MiSTer-devel/CoCo2_MiSTer/rtl/fdc.sv

////////////////////////////////////////////////////////////////////////////////
// Project Name:	COCO3 Targeting MISTer 
// File Name:		fdc.sv
//
// Floppy Disk Controller for MISTer
//
////////////////////////////////////////////////////////////////////////////////
//
// Code based partily on work by Gary Becker
// Copyright (c) 2008 Gary Becker (gary_l_becker@yahoo.com)
//
// Floopy Disk Controller (fdc.v) by Stan Hodge (stan.pda@gmail.com)
// Copyright (c) 2021 by Stan Hodge (stan.pda@gmail.com)
//
// All rights reserved

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
// Redistributions in synthesized form must reproduce the above copyright
// notice, this list of conditions and the following disclaimer in the
// documentation and/or other materials provided with the distribution.
//
// Neither the name of the author nor the names of other contributors may
// be used to endorse or promote products derived from this software without
// specific prior written permission.
//
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
// Please report bugs to the author, but before you do so, please
// make sure that this is not a derivative work and that
// you have the latest version of this file.
//
////////////////////////////////////////////////////////////////////////////////
////////////////////////////////////////////////////////////////////////////////



module fdc(
	input        		CLK,     		// clock
	input        		RESET_N,	   	// async reset
	input					dragon,			// Coco or Dragon ?
	input  		[1:0]	ADDRESS,       	// i/o port addr [extended for coco]
	input  		[7:0]	DATA_IN,        // data in
	output 		[7:0] DATA_HDD,      	// data out
	output       		HALT,         	// DMA request
	output       		NMI_09,
	output       		FIRQ,


	input				FF40_CLK,		// FDC Write support
	input				FF40_ENA,

	input				FF40_RD,		// FDC Read Data support
	input				WD1793_RD,

	input				WD1793_WR_CTRL,	// 1793 RD & WR control signal generation
	input				WD1793_RD_CTRL,

// 	SD block level interface

	input 		[3:0]	img_mounted, 	// signaling that new image has been mounted
	input				img_readonly, 	// mounted as read only. valid only for active bit in img_mounted
	input 		[19:0] 	img_size,    	// size of image in bytes. 1MB MAX!

	output		[31:0] 	sd_lba[4],
	output		[5:0]	sd_blk_cnt[4],	// number of blocks-1, total size ((sd_blk_cnt+1)*(1<<(BLKSZ+7))) must be <= 16384!
	output reg	[3:0]	sd_rd,
	output reg  [3:0]	sd_wr,
	input       [3:0]	sd_ack,

// 	SD byte level access. Signals for 2-PORT altsyncram.
	input  		[8:0]	sd_buff_addr,
	input  		[7:0] 	sd_buff_dout,
	output 		[7:0] 	sd_buff_din[4],
	input        		sd_buff_wr
	
);

wire	[7:0]	DRIVE_SEL_EXT;
wire			MOTOR;
wire			WRT_PREC;
wire			DENSITY;
wire			HALT_EN;


// Generate a 8.333 Mhz enable for the fdc... and control writes 
// Dragon needs a 1.5 Mhz clock

wire ena_8Mhz ; 
wire [6:0] fdc_clk_dvd ;
wire [5:0]	div_8mhz;

// yet another poorly documented difference between Dragon and CoCo2 : clock of the disk controller is 8Mhz for Coco and 1.5Mhz for Dragon
assign fdc_clk_dvd = (dragon ) ? 6'd38 : 6'd6 ;
assign ena_8Mhz = (div_8mhz == fdc_clk_dvd) ? 1'b1: 1'b0;

always@(negedge CLK or negedge RESET_N)
begin
	if (~RESET_N)	div_8mhz <= 6'd0;
	else
		begin
			if (ena_8Mhz)
				div_8mhz <= 6'd0;
			else
				div_8mhz <= div_8mhz + 6'd1;
		end
end


wire	[7:0]	FF40_READ_VALUE =  {HALT_EN, DRIVE_SEL_EXT[3], DENSITY, WRT_PREC, MOTOR,	DRIVE_SEL_EXT[2:0]};

//FDC read data path.  =$ff40 or wd1793(s)
assign	DATA_HDD =		(FF40_RD)							?	FF40_READ_VALUE:
						(WD1793_RD)							?	DATA_1793: //(1793[s])
																8'h00;

// $ff40 control register [part 1]

wire	[3:0]	DRIVE_SEL_EXT_PRE = {DATA_IN[6], DATA_IN[2:0]};
reg		[2:0]	drive_index;

// SD blk system is a array of 4 systems - one for each drive.  
// To keep disk track memory, we created 4 wd1793's to match the sd block interfaces
// For the interface back to the coco - we need to isolate the wd1793 the computer is talking
// to and route those feedback signals back to the coco.  This is accomplished via the drive
// select.  'drive_index' identifies which controller is addressd.


always @(negedge FF40_CLK or negedge RESET_N)
begin
	if(!RESET_N)
	begin
		DRIVE_SEL_EXT <= 8'h00;
		MOTOR <= 1'b0;
		WRT_PREC <= 1'b0;
		DENSITY <= 1'b0;
		drive_index <= 3'b000; 
	end else
	begin
		if (FF40_ENA)
		begin
			if (dragon) 
			begin
//				drive_index <= { ~DATA_IN[2], DATA_IN[1:0] } ; //bit2='0 means no drive selected and no motor 
				drive_index <= { 1'b0, DATA_IN[1:0] } ; // SRH & jF removed motor from causing selects to be out of range 
				MOTOR <= DATA_IN[2];
				DRIVE_SEL_EXT <= DATA_IN ; // only for DRIVE_SEL_EXT[3] for double-density 
				DENSITY <= DATA_IN[5] ;
			end else begin
				DRIVE_SEL_EXT <= 	{4'b0000,
									DATA_IN[6],		// Drive Select [3] / Side Select
									DATA_IN[2:0]};	// Drive Select [2:0]
				MOTOR <= DATA_IN[3];				// Turn on motor, not used here just checked, 0=MotorOff 1=MotorOn
				WRT_PREC <= DATA_IN[4];				// Write Precompensation, not used here
				DENSITY <= DATA_IN[5];				// Density, not used here just checked
				case(DRIVE_SEL_EXT_PRE)
				4'b1000:
					drive_index <= 3'd3;

				4'b0100:
					drive_index <= 3'd2;
			
				4'b0010:
					drive_index <= 3'd1;
				
				4'b0001:
					drive_index <= 3'd0;
				
				4'b1100:
					drive_index <= 3'd2;
				
				4'b1010:
					drive_index <= 3'd1;
				
				4'b1001:
					drive_index <= 3'd0;

				default:
					drive_index <= 3'd0;
				endcase
			end
		end
	end
end

// $ff40 control register [part 2]
always @(negedge FF40_CLK or negedge HALT_EN_RST)
begin
	if(!HALT_EN_RST)
	begin
		HALT_EN <= 1'b0;
	end
	else
	begin
		if (FF40_ENA)
		begin
			HALT_EN <= DATA_IN[7];					// Normal Halt enable, 0=Disabled 1=Enabled
		end
	end
end


// Control signals for the wd1793

wire 			INTRQ[4];
wire			DRQ[4];
wire			selected_DRQ;
wire			selected_INTRQ;

wire			WR[4];
wire			RD[4];
wire			RD_E[4];
//wire			CE;
wire			HALT_EN_RST;
wire	[7:0]	DATA_1793;
wire	[7:0]	dout[4];
reg				read;
reg				write;
reg 			read_d;
reg				write_d;
reg		[7:0]	DATA_IN_L;
reg				r_w_active;
reg				clk_8Mhz_enable_found;
reg				read1;
reg				write1;
reg		[1:0]	ADDRESS_L;

assign RD[0] = (read || RD_E[0])  && (drive_index == 3'd0);
assign RD[1] = (read || RD_E[1])  && (drive_index == 3'd1);
assign RD[2] = (read || RD_E[2])  && (drive_index == 3'd2);
assign RD[3] = (read || RD_E[3])  && (drive_index == 3'd3);

// The idea here is to "stretch" the CPU read and write signals to ensure we catch a 8 mhz enable.
// For writes we will buffer the data out to ensure it does not go away.
// For reads it is expected that data is available asynchronusly at the cpu rate and the only reason to catch a 
// 8Mhz edge is to update pointer and misc flags. 

// This is very nasty code and will likely only work with the present CPU timing.
// It is heavily dependant on address and write data being available just after
// the previous cycle.

always @(negedge CLK or negedge RESET_N)
begin
	if(!RESET_N)
	begin
		read_d <= 1'b0;
		write_d <= 1'b0;
		r_w_active <= 1'b0;
		clk_8Mhz_enable_found <= 1'b0;
		WR[0] <= 1'b0;
		WR[1] <= 1'b0;
		WR[2] <= 1'b0;
		WR[3] <= 1'b0;
		RD_E[0] <= 1'b0;
		RD_E[1] <= 1'b0;
		RD_E[2] <= 1'b0;
		RD_E[3] <= 1'b0;
		read1 <= 1'b0;
		write1 <= 1'b0;
		read <= 1'b0;
		write <= 1'b0;
	end
	else
	begin

//		synchronizers
		read1 <= WD1793_RD_CTRL;
		read <= read1;
		
		write1 <= WD1793_WR_CTRL;
		write <= write1;

//		delays for edge detection
		read_d <= read;
		write_d <= write;

		if ((read1 & ~read) | (write1 & ~write))
		begin
//			Latch Address & Data
			ADDRESS_L <= ADDRESS[1:0];
			DATA_IN_L <= DATA_IN;
		end
		
//		Synchronus rising edge of write
		if ((write == 1'b1) && (write_d == 1'b0))
		begin
//			Set Writes
			r_w_active <= 1'b1;
			if (ADDRESS[1:0]==2'b00)
				case (drive_index)
					3'd0:
						WR[0] <= 1'b1;
					3'd1:
						WR[1] <= 1'b1;
					3'd2:
						WR[2] <= 1'b1;
					3'd3:
						WR[3] <= 1'b1;
				endcase 
			else 
			begin // FLYNN : if not a command, write the register in ALL fdc components.
				WR[0] <= 1'b1;
				WR[1] <= 1'b1;
				WR[2] <= 1'b1;
				WR[3] <= 1'b1;
			end
		end

//		Synchronus rising edge of read
		if ((read == 1'b1) && (read_d == 1'b0))
		begin
			r_w_active <= 1'b1;
			case (drive_index)
				3'd0:
					RD_E[0] <= 1'b1;
				3'd1:
					RD_E[1] <= 1'b1;
				3'd2:
					RD_E[2] <= 1'b1;
				3'd3:
					RD_E[3] <= 1'b1;
			endcase
		end

//		Clears
		if (ena_8Mhz && r_w_active)
			clk_8Mhz_enable_found <= 1'b1;

//		1 50Mhz clock later...
		if (clk_8Mhz_enable_found)
		begin
			clk_8Mhz_enable_found <= 1'b0;
			r_w_active <= 1'b0;
			
			WR[0] <= 1'b0;
			WR[1] <= 1'b0;
			WR[2] <= 1'b0;
			WR[3] <= 1'b0;

			RD_E[0] <= 1'b0;
			RD_E[1] <= 1'b0;
			RD_E[2] <= 1'b0;
			RD_E[3] <= 1'b0;
		end
	end
end


//	NMI from disk controller
//	Selected INTRQ
assign	selected_INTRQ	=	(drive_index == 3'd0)	?	INTRQ[0]:
							(drive_index == 3'd1)	?	INTRQ[1]:
							(drive_index == 3'd2)	?	INTRQ[2]:
							(drive_index == 3'd3)	?	INTRQ[3]:
														1'b0;

assign	NMI_09	=  DENSITY & selected_INTRQ;				// DENSITY is just the IRQ mask : Send NMI if allowed (Halt Mode)

//	HALT from disk controller
//	Selected DRQ
assign FIRQ = selected_DRQ;

assign	selected_DRQ	=	(drive_index == 3'd0)	?	DRQ[0]:
							(drive_index == 3'd1)	?	DRQ[1]:
							(drive_index == 3'd2)	?	DRQ[2]:
							(drive_index == 3'd3)	?	DRQ[3]:
														1'b0;

assign	HALT	=	HALT_EN & ~selected_DRQ;

assign	HALT_EN_RST = RESET_N & ~selected_INTRQ; // From controller schematic

// Data bus selection
assign	DATA_1793 	=		(drive_index == 3'd0)	?	dout[0]:
							(drive_index == 3'd1)	?	dout[1]:
							(drive_index == 3'd2)	?	dout[2]:
							(drive_index == 3'd3)	?	dout[3]:
														8'd0;

// The SD_BLK interface and thus the wd1793 will allways transfer 1 blk. This is blk qty - 1 per spec.
assign sd_blk_cnt[3] = 6'd0;
assign sd_blk_cnt[2] = 6'd0;
assign sd_blk_cnt[1] = 6'd0;
assign sd_blk_cnt[0] = 6'd0;

reg       drive_wp[4];
reg       [3:0] drive_ready  = 4'B0;
reg       [3:0] double_sided = 4'B0;

wire [3:0] img_mounted_d ;

// As drives are mounted in MISTer this logic saves the write protect and generates ready for
// changing drives to the wd1793.
// This can also get the disk size to properly handle DS drives - TBD

// Reset of drive wp to a default of 1 removed because of persistance.

// Drive 0

always @(negedge CLK)
begin
   img_mounted_d[0] <= img_mounted[0] ;
	if (img_mounted[0] & ~img_mounted_d[0]) begin
		drive_wp[0] <= img_readonly;
		drive_ready[0] <= (img_size!=20'd0) ; 
		// drive_ready[0] <= 1'b1;
		double_sided[0]<= img_size > 20'd368600;//20'd368640;
	end
end

// Drive 1

always @(negedge CLK)
begin
   img_mounted_d[1] <= img_mounted[1] ;
	if (img_mounted[1] & ~img_mounted_d[1]) begin
		drive_wp[1] <= img_readonly;
		drive_ready[1] <= (img_size!=20'd0) ; 
		double_sided[1]<= img_size > 20'd368600;//20'd368640;
	end
end

// Drive 2

always @(negedge CLK)
begin
   img_mounted_d[2] <= img_mounted[2] ;
	if (img_mounted[2] & ~img_mounted_d[2]) begin
		drive_wp[2] <= img_readonly;
		drive_ready[2] <= (img_size!=20'd0) ; 
		double_sided[2]<= img_size > 20'd368600;//20'd368640;
	end
end

// Drive 3

always @(negedge CLK)
begin
   img_mounted_d[3] <= img_mounted[3] ;
	if (img_mounted[3] & ~img_mounted_d[3]) begin
		drive_wp[3] <= img_readonly;
		drive_ready[3] <= (img_size!=20'd0) ; 
		double_sided[3]<= img_size > 20'd368600;//20'd368640;
	end
end


wd1793 #(1,1) coco_wd1793_0
(
	.clk_sys(~CLK),
	.ce(ena_8Mhz),
	.reset(~RESET_N),
	.io_en(1'b1),
	.rd(RD[0]),
	.wr(WR[0]),
	.addr(ADDRESS_L[1:0]),
	.din(DATA_IN_L),
	.dout(dout[0]),
	.drq(DRQ[0]),
	.intrq(INTRQ[0]),
	.dragon(dragon),

	.img_mounted(img_mounted[0]),
	.img_size(img_size),

	.sd_lba(sd_lba[0]),
	.sd_rd(sd_rd[0]),
	.sd_wr(sd_wr[0]), 
	.sd_ack(sd_ack[0]),

	.sd_buff_addr(sd_buff_addr),
	.sd_buff_dout(sd_buff_dout),
	.sd_buff_din(sd_buff_din[0]), 
	.sd_buff_wr(sd_buff_wr),

	.wp(drive_wp[0]),

	.size_code(3'd5),		// 5 is 18 sector x 256 bits COCO standard
	.layout(~double_sided[0]),	// 0 = Track-Side-Sector, 1 - Side-Track-Sector
	.coco_side(double_sided[0] & DRIVE_SEL_EXT[3]), // CoCo specific floppy side signal
 	.ready(drive_ready[0]),

	.input_active(0),
	.input_addr(0),
	.input_data(0),
	.input_wr(0),
	.buff_din(0)
);

wd1793 #(1,0) coco_wd1793_1
(
	.clk_sys(~CLK),
	.ce(ena_8Mhz),
	.reset(~RESET_N),
	.io_en(1'b1),
	.rd(RD[1]),
	.wr(WR[1]),
	.addr(ADDRESS_L[1:0]),
	.din(DATA_IN_L),
	.dout(dout[1]),
	.drq(DRQ[1]),
	.intrq(INTRQ[1]),
	.dragon(dragon),

	.img_mounted(img_mounted[1]),
	.img_size(img_size),

	.sd_lba(sd_lba[1]),
	.sd_rd(sd_rd[1]),
	.sd_wr(sd_wr[1]), 
	.sd_ack(sd_ack[1]),

	.sd_buff_addr(sd_buff_addr),
	.sd_buff_dout(sd_buff_dout),
	.sd_buff_din(sd_buff_din[1]), 
	.sd_buff_wr(sd_buff_wr),

	.wp(drive_wp[1]),

	.size_code(3'd5),		// 5 is 18 sector x 256 bits COCO standard
	.layout(~double_sided[1]),	// 0 = Track-Side-Sector, 1 - Side-Track-Sector
	.coco_side(double_sided[1] & DRIVE_SEL_EXT[3]), // CoCo specific floppy side signal
	.ready(drive_ready[1]),

	.input_active(0),
	.input_addr(0),
	.input_data(0),
	.input_wr(0),
	.buff_din(0)
);

wd1793 #(1,0) coco_wd1793_2
(
	.clk_sys(~CLK),
	.ce(ena_8Mhz),
	.reset(~RESET_N),
	.io_en(1'b1),
	.rd(RD[2]),
	.wr(WR[2]),
	.addr(ADDRESS_L[1:0]),
	.din(DATA_IN_L),
	.dout(dout[2]),
	.drq(DRQ[2]),
	.intrq(INTRQ[2]),
	.dragon(dragon),

	.img_mounted(img_mounted[2]),
	.img_size(img_size),

	.sd_lba(sd_lba[2]),
	.sd_rd(sd_rd[2]),
	.sd_wr(sd_wr[2]), 
	.sd_ack(sd_ack[2]),

	.sd_buff_addr(sd_buff_addr),
	.sd_buff_dout(sd_buff_dout),
	.sd_buff_din(sd_buff_din[2]), 
	.sd_buff_wr(sd_buff_wr),

	.wp(drive_wp[2]),

	.size_code(3'd5),		// 5 is 18 sector x 256 bits COCO standard
	.layout(~double_sided[2]),	// 0 = Track-Side-Sector, 1 - Side-Track-Sector
	.coco_side(double_sided[2] & DRIVE_SEL_EXT[3]), // CoCo specific floppy side signal
	.ready(drive_ready[2]),

	.input_active(0),
	.input_addr(0),
	.input_data(0),
	.input_wr(0),
	.buff_din(0)
);

wd1793 #(1,0) coco_wd1793_3
(
	.clk_sys(~CLK),
	.ce(ena_8Mhz),
	.reset(~RESET_N),
	.io_en(1'b1),
	.rd(RD[3]),
	.wr(WR[3]),
	.addr(ADDRESS_L[1:0]),
	.din(DATA_IN_L),
	.dout(dout[3]),
	.drq(DRQ[3]),
	.intrq(INTRQ[3]),
	.dragon(dragon),

	.img_mounted(img_mounted[3]),
	.img_size(img_size),

	.sd_lba(sd_lba[3]),
	.sd_rd(sd_rd[3]),
	.sd_wr(sd_wr[3]), 
	.sd_ack(sd_ack[3]),

	.sd_buff_addr(sd_buff_addr),
	.sd_buff_dout(sd_buff_dout),
	.sd_buff_din(sd_buff_din[3]), 
	.sd_buff_wr(sd_buff_wr),

	.wp(drive_wp[3]),

	.size_code(3'd5),		// 5 is 18 sector x 256 bits COCO standard
	.layout((dragon) ? ~double_sided[3] : 1'b1),			// 0 = Track-Side-Sector, 1 - Side-Track-Sector
	.coco_side(1'b0),			// CoCo only : DS can not be supported for drive 3.
	.ready(drive_ready[3]),

	.input_active(0),
	.input_addr(0),
	.input_data(0),
	.input_wr(0),
	.buff_din(0)
);

endmodule
